BoujeeEnjinia1701/picoflow/cad/drawings/PCF-DWG-101.pdf

### BUILD PLAN SKETCH, PLAN NOT YET BUILT PicoFlow · github.com/BoujeeEnjinia1701/picoflow

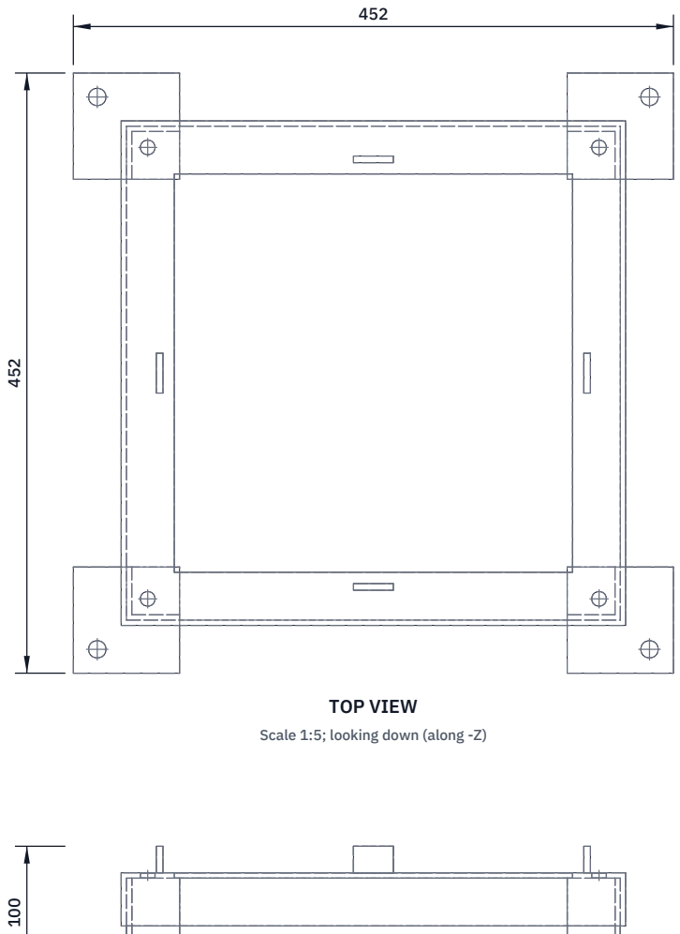
[picture p7: figure]
TOP VIEW; Scale 1:5; looking down (along -Z)

FRONT VIEW
Scale 1:5; looking at the front (along +Y)

RIGHT VIEW
Scale 1:5; looking at the right side (along -X)

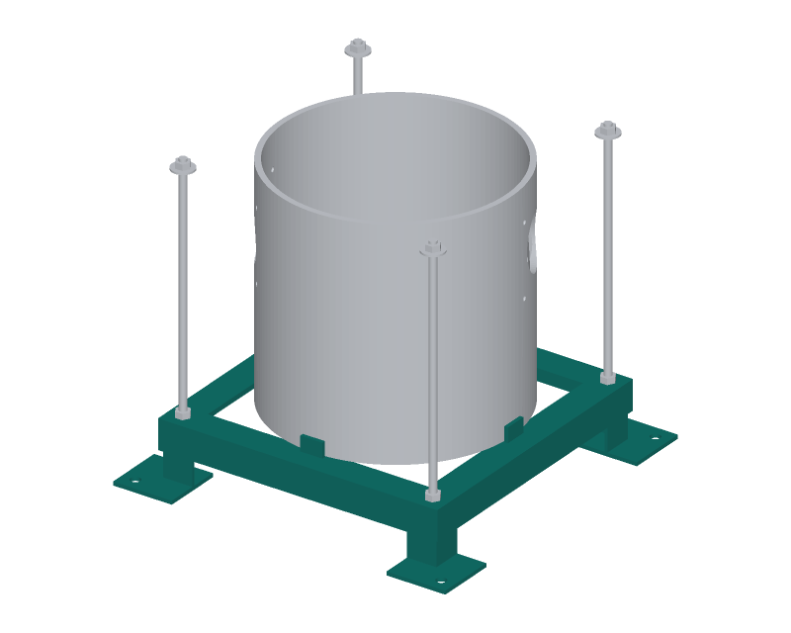
[picture p8: figure]

WHERE IT GOES
This part in colour, its neighbours in grey

HOW TO MAKE IT AND HOW IT FITS
Square: four 380 mm lengths of 40 x 40 x 4 angle, mitred 45 deg at each end, horizontal legs pointing inward, top faces flat and level.
Weld the corners; check the diagonals agree within 2 mm.
Legs: four 70 mm lengths of the same angle, fitted inside each corner, tight under the horizontal legs and against the vertical legs; weld.
Feet: four 80 x 80 x 5 mm plates welded under the legs, reaching outward; one 13 mm anchor hole in each, 208 mm from the centre lines. Pipe stops: four 30 x 20 x 5 mm flat bars welded upright on the horizontal legs at the middle of each side, inner face 158.5 mm
from the centre (1 mm outside the housing).
Tie rod holes: 11 mm in each corner, 170 mm from both centre lines.
Clean the welds, then galvanize or paint the whole frame. Never weld after galvanizing. Check: top flat within 1 mm; the housing drops in between the stops.
REV | DESCRIPTION | DATE | BY
P1 | Making sketch for the prototype build plan | 2026-10-02 | AC
PICOFLOW | github.com/BoujeeEnjinia1701/picoflow

## PicoFlow turbine frame: making sketch

DRAWING NO.
PCF-DWG-101

REV
P1

SHEET
1 of 1

SIZE

## ANSI B

SCALE
1:5

UNITS
mm
PROJECTION | DATE
2026-10-02

DRAWN
Amish Chadha

MATERIAL / NOTES
Bare steel angle 40 x 40 x 4 mm; flat 80 x 80 x 5 and 30 x 20 x 5 mm; galvanized or painted after welding
Licensed CERN-OHL-S-2.0 · Design Molecule Lab · designmolecule.com | Generated from cad/src; do not edit by hand
