BoujeeEnjinia1701/picoflow/cad/drawings/PCF-DWG-102.pdf

### BUILD PLAN SKETCH, PLAN NOT YET BUILT PicoFlow · github.com/BoujeeEnjinia1701/picoflow

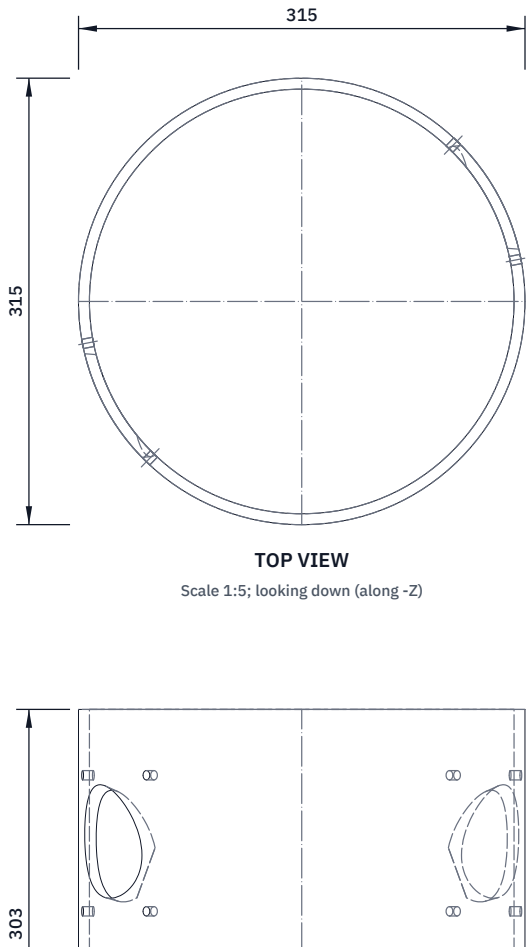
[picture p9: figure]
TOP VIEW; Scale 1:5; looking down (along -Z)

FRONT VIEW
Scale 1:5; looking at the front (along +Y)

RIGHT VIEW
Scale 1:5; looking at the right side (along -X)

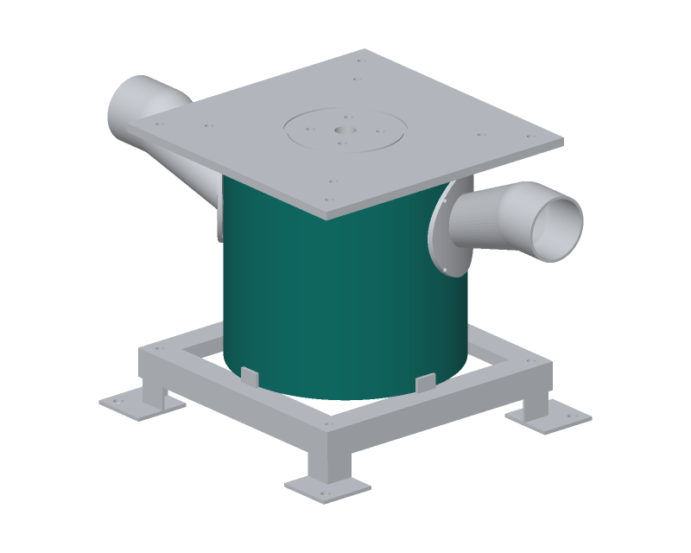
[picture p10: figure]

WHERE IT GOES
This part in colour, its neighbours in grey

HOW TO MAKE IT AND HOW IT FITS
Cut 303 mm of 315 mm pipe. Wrap a strip of card round the pipe as a guide, saw square with a fine-tooth saw, and file both ends flat.
Two nozzle holes, on opposite sides, each with four bolt holes. Tape the full-size template (nozzle hole template) to the pipe: its centre line
is 208.6 mm up from the bottom end; the second hole is the same, turned half a turn round the pipe.
Chain drill inside the hole outline with 6 mm, cut out with a jigsaw, file to the line. Drill the eight bolt holes 6.6 mm square to the wall. The holes are larger than the nozzle tip by 2.5 mm all round; the nozzle saddle and its gasket cover them.
The 3 mm at the top sits in the groove under the lid.
Check: each nozzle passes through its hole without touching the edge.
REV | DESCRIPTION | DATE | BY
P1 | Making sketch for the prototype build plan | 2026-10-02 | AC
PICOFLOW | github.com/BoujeeEnjinia1701/picoflow

## PicoFlow housing: making sketch

DRAWING NO.
PCF-DWG-102

REV
P1

SHEET
1 of 1

SIZE

## ANSI B

SCALE
1:5

UNITS
mm
PROJECTION | DATE
2026-10-02

DRAWN
Amish Chadha

MATERIAL / NOTES
315 mm PVC sewer pipe, SN4 (7.7 mm wall)
Licensed CERN-OHL-S-2.0 · Design Molecule Lab · designmolecule.com | Generated from cad/src; do not edit by hand
