BoujeeEnjinia1701/picoflow/cad/drawings/PCF-DWG-103.pdf

### BUILD PLAN SKETCH, PLAN NOT YET BUILT PicoFlow · github.com/BoujeeEnjinia1701/picoflow

FRONT VIEW
Scale 1:5; looking at the front (along +Y)

TOP VIEW
Scale 1:5; looking down (along -Z)

RIGHT VIEW
Scale 1:5; looking at the right side (along -X)

244

130 167

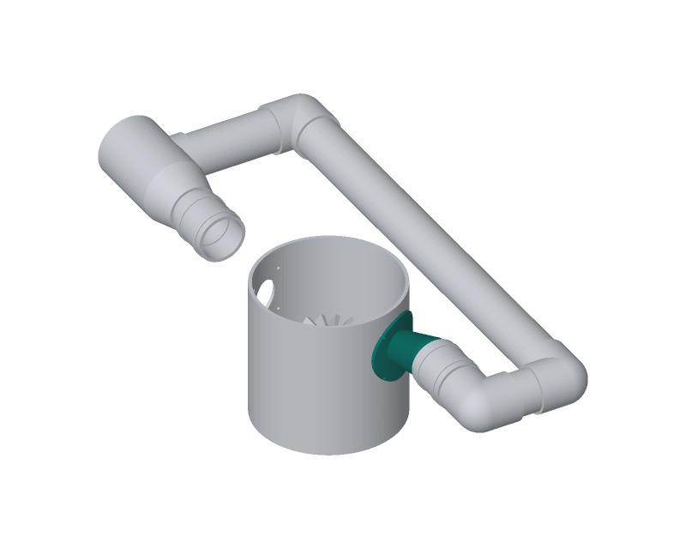
[picture p11: figure]

WHERE IT GOES
This part in colour, its neighbours in grey

HOW TO MAKE IT AND HOW IT FITS
Print two from the model file (cad/step/picoflow-nozzle.step). They are the same part: jet 2's nozzle is jet 1's turned half a turn.
Print standing on the spigot end, with supports under the saddle;
the part fits a 167 x 130 x 244 mm space, about 300 g and 12 h each. Spigot: 90 mm outside, 60 mm long, horizontal. A gentle 20 deg bend turns the nozzle down to the runner. Cone 170 mm long, from 90 mm to 64 mm outside. Saddle: a patch 144 mm across shaped to the housing, 6 mm thick, four 6.6 mm bolt holes.
Tip: a 50 mm seat 25 mm deep for the insert, and two 5.6 mm holes for M4 heat-set inserts, 28.5 mm each side of the centre.
Fit: the tip goes through the housing hole; the saddle sits on a 2 mm EPDM gasket, four M6 bolts, nuts inside. The spigot joins the pipe in a 90 mm flexible coupling.
Check: spigot 90 mm (fits the coupling); saddle sits on the pipe.
REV | DESCRIPTION | DATE | BY
P1 | Making sketch for the prototype build plan | 2026-10-02 | AC
PICOFLOW | github.com/BoujeeEnjinia1701/picoflow

## PicoFlow nozzle (make 2, both the same): making sketch

DRAWING NO.
PCF-DWG-103

REV
P1

SHEET
1 of 1

SIZE

## ANSI B

SCALE
1:5

UNITS
mm
PROJECTION | DATE
2026-10-02

DRAWN
Amish Chadha

MATERIAL / NOTES
PETG, 3D printed, 4 mm walls, 40 % infill
Licensed CERN-OHL-S-2.0 · Design Molecule Lab · designmolecule.com | Generated from cad/src; do not edit by hand
