BoujeeEnjinia1701/picoflow/cad/drawings/PCF-DWG-104.pdf

### BUILD PLAN SKETCH, PLAN NOT YET BUILT PicoFlow · github.com/BoujeeEnjinia1701/picoflow

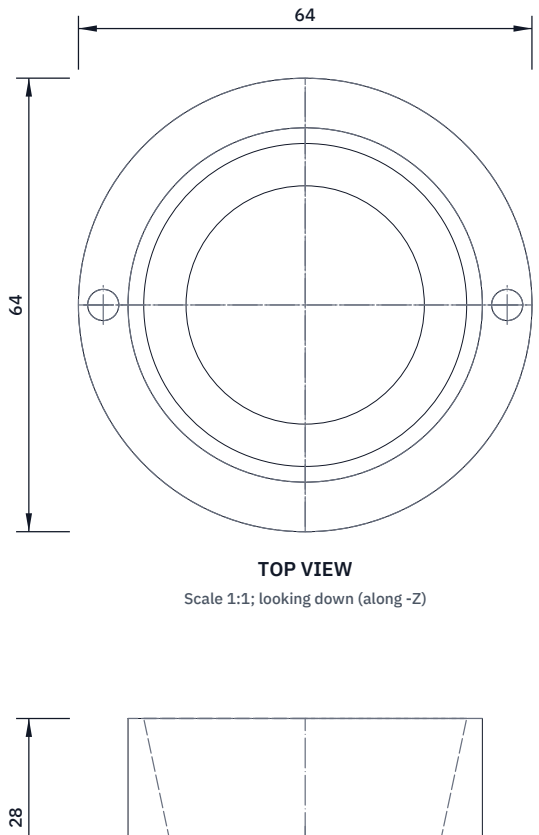
[picture p12: figure]
TOP VIEW; Scale 1:1; looking down (along -Z)

FRONT VIEW
Scale 1:1; looking at the front (along +Y)

RIGHT VIEW
Scale 1:1; looking at the right side (along -X)

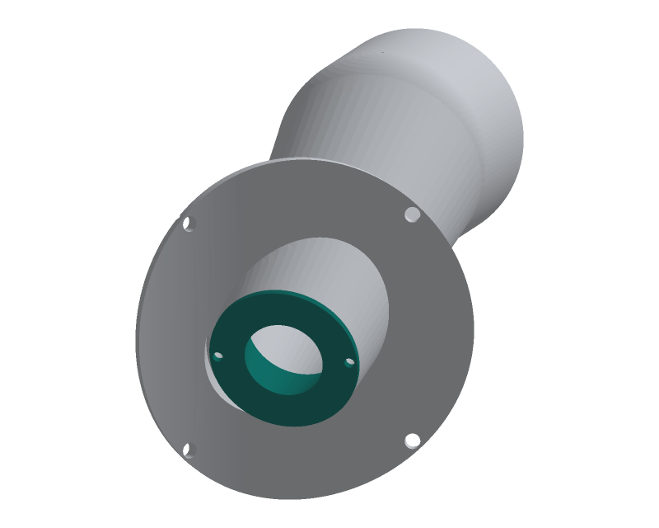
[picture p13: figure]

WHERE IT GOES
This part in colour, its neighbours in grey

HOW TO MAKE IT AND HOW IT FITS
Print a pair for each size used: 34 mm bore for the design point.
A set from 20 to 45 mm covers the head and flow range.
Body: 50 mm outside, 25 mm long, fits the seat in the nozzle tip. Flange: 64 mm across, 3 mm thick, with two 4.4 mm holes 57 mm apart. Bore: converges smoothly from 46 mm at the back to the jet size at
the front face; the last few millimetres must be round and sharp.
Print with the front face down on the bed so the jet edge is clean.
Ream or sand the bore to size; check it with a caliper.
Fit: slide into the nozzle tip from inside the housing, two M4 screws into the heat-set inserts.
Check: the bore is within 0.2 mm of size and round.
REV | DESCRIPTION | DATE | BY
P1 | Making sketch for the prototype build plan | 2026-10-02 | AC
PICOFLOW | github.com/BoujeeEnjinia1701/picoflow

## PicoFlow nozzle insert (make 2 per size): making sketch

DRAWING NO.
PCF-DWG-104

REV
P1

SHEET
1 of 1

SIZE

## ANSI B

SCALE
1:1

UNITS
mm
PROJECTION | DATE
2026-10-02

DRAWN
Amish Chadha

MATERIAL / NOTES
PETG, 3D printed, 100 % infill
Licensed CERN-OHL-S-2.0 · Design Molecule Lab · designmolecule.com | Generated from cad/src; do not edit by hand
