BoujeeEnjinia1701/picoflow/cad/drawings/PCF-DWG-105.pdf

### BUILD PLAN SKETCH, PLAN NOT YET BUILT PicoFlow · github.com/BoujeeEnjinia1701/picoflow

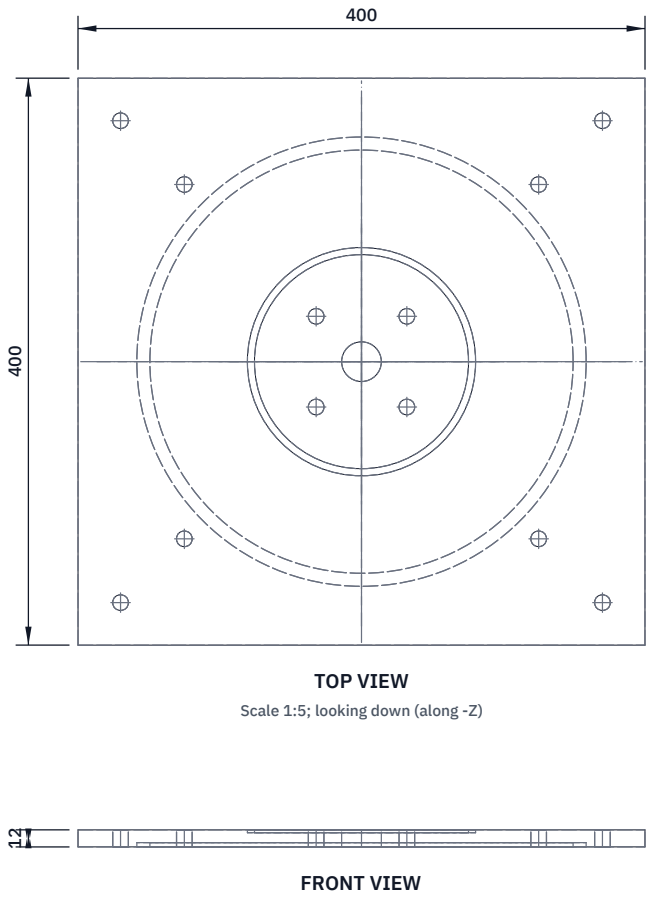
[picture p14: figure]
FRONT VIEW; TOP VIEW; Scale 1:5; looking down (along -Z)

Scale 1:5; looking at the front (along +Y)

RIGHT VIEW
Scale 1:5; looking at the right side (along -X)

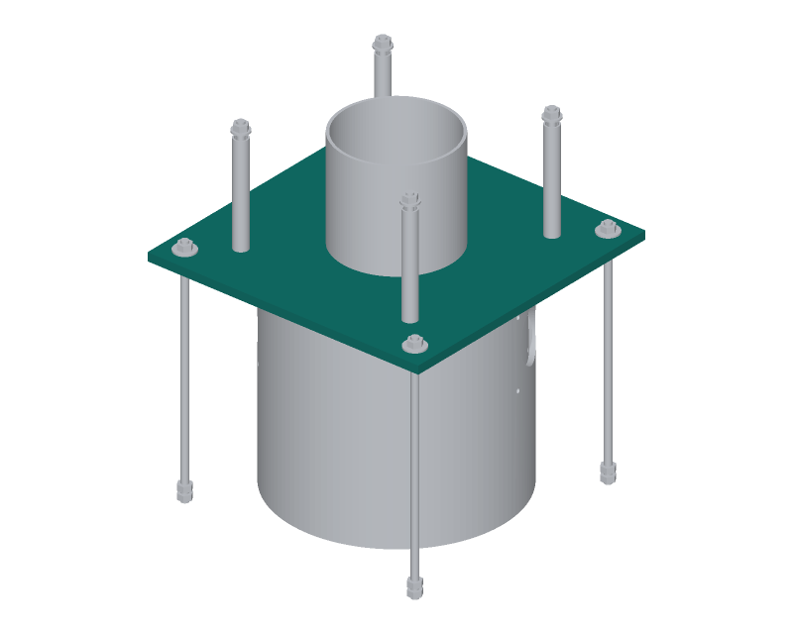
[picture p15: figure]

WHERE IT GOES
This part in colour, its neighbours in grey

HOW TO MAKE IT AND HOW IT FITS
Cut 400 x 400 mm; round the corners to about 5 mm.
Holes from the centre (the lid hole layout figure gives all of them): shaft 28 mm in the centre; bearing bolts 11 mm at 32 each way;
post rods 11 mm at 125 each way; tie rods 11 mm at 170 each way. Underneath: a ring groove 3 mm deep, 148.8 to 158.5 mm radius, that the top of the housing sits in. Rout with a trammel jig.
On top: a ring groove 2 mm deep, 75.5 to 80.5 mm radius, for the guard. Mark the two grooves from the same centre as the shaft hole.
Fit: housing in the lower groove; lower bearing unit, posts and guard on top; four tie rods through the corners with washers and nuts.
Check: the lid drops onto the housing and the groove takes the whole rim without forcing.
REV | DESCRIPTION | DATE | BY
P1 | Making sketch for the prototype build plan | 2026-10-02 | AC
PICOFLOW | github.com/BoujeeEnjinia1701/picoflow

## PicoFlow lid: making sketch

DRAWING NO.
PCF-DWG-105

REV
P1

SHEET
1 of 1

SIZE

## ANSI B

SCALE
1:5

UNITS
mm
PROJECTION | DATE
2026-10-02

DRAWN
Amish Chadha

MATERIAL / NOTES
HDPE sheet 12 mm (or marine plywood, sealed)
Licensed CERN-OHL-S-2.0 · Design Molecule Lab · designmolecule.com | Generated from cad/src; do not edit by hand
