BoujeeEnjinia1701/picoflow/cad/drawings/PCF-DWG-106.pdf

### BUILD PLAN SKETCH, PLAN NOT YET BUILT PicoFlow · github.com/BoujeeEnjinia1701/picoflow

FRONT VIEW
Scale 1:2; looking at the front (along +Y)

TOP VIEW
Scale 1:2; looking down (along -Z)

RIGHT VIEW
Scale 1:2; looking at the right side (along -X)

294

20 20

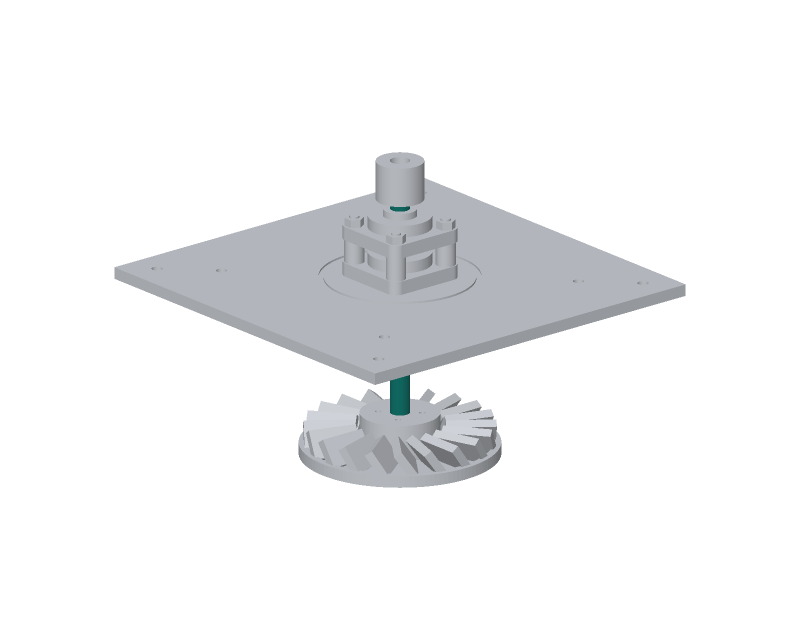
[picture p16: figure]

WHERE IT GOES
This part in colour, its neighbours in grey

HOW TO MAKE IT AND HOW IT FITS
Cut 294 mm of 20 mm ground stainless bar; face both ends square and chamfer them 1 mm so the bearings slide on.
Check the bar slides through a bearing unit by hand; polish any burr with fine emery.
No keyways: the runner hub and coupling clamp the shaft, and the bearing inserts lock with their own set screws.
At assembly, spot each set screw into the shaft with a 5 mm drill 0.5 mm deep through the screw hole, then tighten.
Fit: bottom end flush with the underside of the runner hub; top end half way into the jaw coupling, 30 mm above the upper bearing. Check: straight within 0.1 mm over its length (roll it on glass).
REV | DESCRIPTION | DATE | BY
P1 | Making sketch for the prototype build plan | 2026-10-02 | AC
PICOFLOW | github.com/BoujeeEnjinia1701/picoflow

## PicoFlow shaft: making sketch

DRAWING NO.
PCF-DWG-106

REV
P1

SHEET
1 of 1

SIZE

## ANSI B

SCALE
1:2

UNITS
mm
PROJECTION | DATE
2026-10-02

DRAWN
Amish Chadha

MATERIAL / NOTES
316 stainless steel bar, 20 mm, h9 or ground
Licensed CERN-OHL-S-2.0 · Design Molecule Lab · designmolecule.com | Generated from cad/src; do not edit by hand
