BoujeeEnjinia1701/picoflow/cad/drawings/PCF-DWG-107.pdf

### BUILD PLAN SKETCH, PLAN NOT YET BUILT PicoFlow · github.com/BoujeeEnjinia1701/picoflow

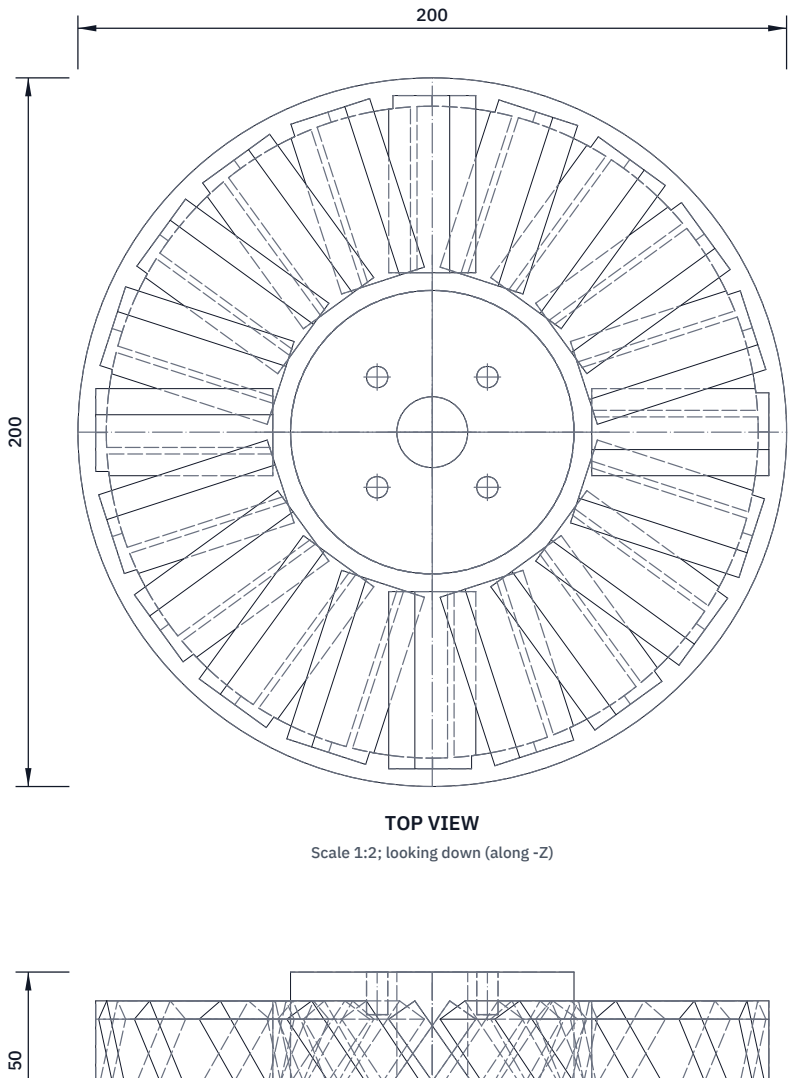
[picture p17: figure]
TOP VIEW; Scale 1:2; looking down (along -Z)

FRONT VIEW
Scale 1:2; looking at the front (along +Y)

RIGHT VIEW
Scale 1:2; looking at the right side (along -X)

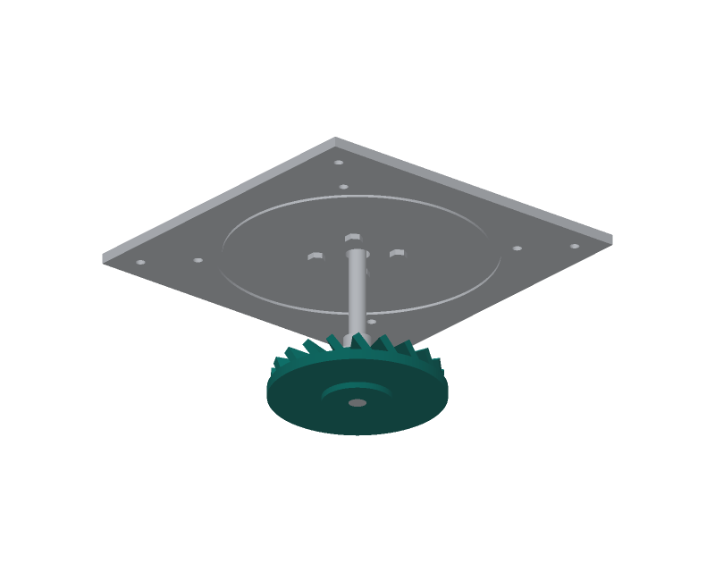
[picture p18: figure]

WHERE IT GOES
This part in colour, its neighbours in grey

HOW TO MAKE IT AND HOW IT FITS
Print from the model file (cad/step/picoflow-runner.step), hub down, with supports under the buckets. 200 mm across, 50 mm tall,
about 525 g and 21 h at 0.4 mm; four perimeters.
20 buckets on a 150 mm pitch circle; the jets strike the top of the bucket band, which is 17 mm above the runner's mid-height.
Hub: 80 mm across, 50 mm tall, 20 mm bore. Ream the bore to slide on the shaft. Press four M5 heat-set inserts into the hub top on
a 44 mm circle with a soldering iron.
Balance: hang the runner on a rod through the bore; if one side always drops, sand the bucket backs on that side lightly.
Fit: the clamping hub bolts to the hub top with four M5 screws. Check: the runner spins on a rod and stops in random places.
REV | DESCRIPTION | DATE | BY
P1 | Making sketch for the prototype build plan | 2026-10-02 | AC
PICOFLOW | github.com/BoujeeEnjinia1701/picoflow

## PicoFlow Turgo runner: making sketch

DRAWING NO.
PCF-DWG-107

REV
P1

SHEET
1 of 1

SIZE

## ANSI B

SCALE
1:2

UNITS
mm
PROJECTION | DATE
2026-10-02

DRAWN
Amish Chadha

MATERIAL / NOTES
PETG (prototype), glass-filled nylon (field)
Licensed CERN-OHL-S-2.0 · Design Molecule Lab · designmolecule.com | Generated from cad/src; do not edit by hand
