BoujeeEnjinia1701/picoflow/cad/drawings/PCF-DWG-108.pdf

### BUILD PLAN SKETCH, PLAN NOT YET BUILT PicoFlow · github.com/BoujeeEnjinia1701/picoflow

FRONT VIEW
Scale 1:5; looking at the front (along +Y)

TOP VIEW
Scale 1:5; looking down (along -Z)

RIGHT VIEW
Scale 1:5; looking at the right side (along -X)

160

160 146

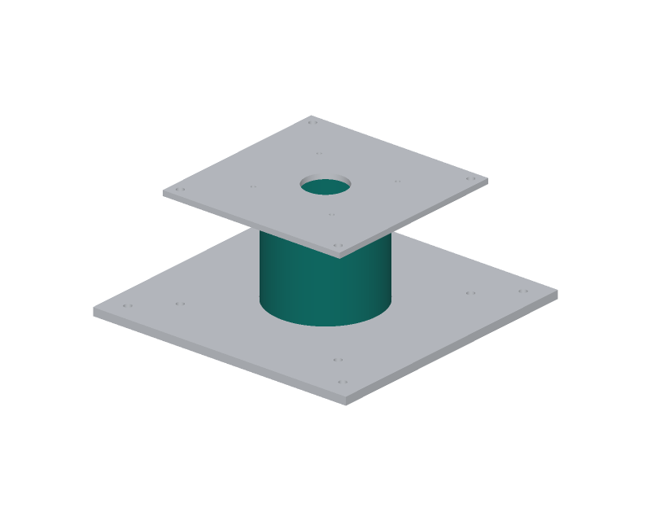
[picture p19: figure]

WHERE IT GOES
This part in colour, its neighbours in grey

HOW TO MAKE IT AND HOW IT FITS
Cut 146 mm of 160 mm pipe; saw square, file both ends flat and deburr inside.
Drill two 6 mm holes at the bottom edge, on opposite sides, so any water that gets in drains out.
Fit: the bottom end stands in the 2 mm groove on top of the lid; the top end stops 1 mm under the generator plate, which holds it in place. It covers both bearing units and the jaw coupling; nothing that turns can be reached while the plate is on.
Check: it stands in the groove and the plate clears it.
REV | DESCRIPTION | DATE | BY
P1 | Making sketch for the prototype build plan | 2026-10-02 | AC
PICOFLOW | github.com/BoujeeEnjinia1701/picoflow

## PicoFlow bearing and coupling guard: making sketch

DRAWING NO.
PCF-DWG-108

REV
P1

SHEET
1 of 1

SIZE

## ANSI B

SCALE
1:5

UNITS
mm
PROJECTION | DATE
2026-10-02

DRAWN
Amish Chadha

MATERIAL / NOTES
160 mm PVC pipe, 4 mm wall
Licensed CERN-OHL-S-2.0 · Design Molecule Lab · designmolecule.com | Generated from cad/src; do not edit by hand
