BoujeeEnjinia1701/picoflow/cad/drawings/PCF-DWG-109.pdf

### BUILD PLAN SKETCH, PLAN NOT YET BUILT PicoFlow · github.com/BoujeeEnjinia1701/picoflow

FRONT VIEW
Scale 1:2; looking at the front (along +Y)

TOP VIEW
Scale 1:2; looking down (along -Z)

RIGHT VIEW
Scale 1:2; looking at the right side (along -X)

20

20 145

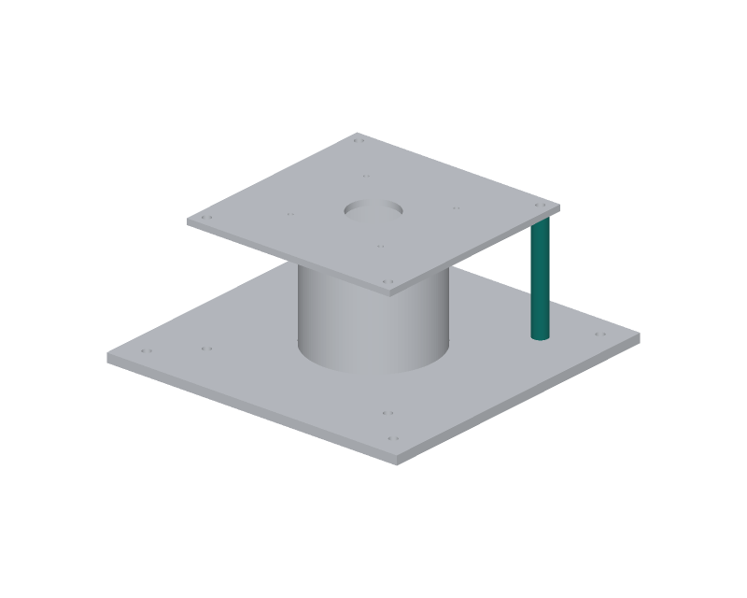
[picture p20: figure]

WHERE IT GOES
This part in colour, its neighbours in grey

HOW TO MAKE IT AND HOW IT FITS
Posts: cut four 145.0 mm lengths of 20 x 2 mm steel tube. Face the ends square on a disc sander; all four the same within 0.2 mm,
so the plate sits level.
Post rods: cut four 195 mm lengths of M10 rod; clean the thread ends. Bearing spacer sleeves: cut four 24.0 mm lengths of 20 mm tube with a 10.5 mm or larger bore, the same within 0.1 mm.
Tie rods: cut four 345 mm lengths of M10 rod.
Paint or galvanize the cut ends.
Fit: each post stands on the lid at 125 mm each way from the centre; the rod goes up from under the lid, through the post and the plate, with a 30 mm washer and nut under the lid and a washer and nut on the plate.
Check: the four posts stand the same height on a flat surface.
REV | DESCRIPTION | DATE | BY
P1 | Making sketch for the prototype build plan | 2026-10-02 | AC
PICOFLOW | github.com/BoujeeEnjinia1701/picoflow

## PicoFlow post and spacer sleeve (make 4 of each): making sketch

DRAWING NO.
PCF-DWG-109

REV
P1

SHEET
1 of 1

SIZE

## ANSI B

SCALE
1:2

UNITS
mm
PROJECTION | DATE
2026-10-02

DRAWN
Amish Chadha

MATERIAL / NOTES
Steel tube 20 x 2 mm; M10 threaded rod
Licensed CERN-OHL-S-2.0 · Design Molecule Lab · designmolecule.com | Generated from cad/src; do not edit by hand
