BoujeeEnjinia1701/picoflow/cad/drawings/PCF-DWG-110.pdf

### BUILD PLAN SKETCH, PLAN NOT YET BUILT PicoFlow · github.com/BoujeeEnjinia1701/picoflow

FRONT VIEW
Scale 1:5; looking at the front (along +Y)

TOP VIEW
Scale 1:5; looking down (along -Z)

RIGHT VIEW
Scale 1:5; looking at the right side (along -X)

280

280 8

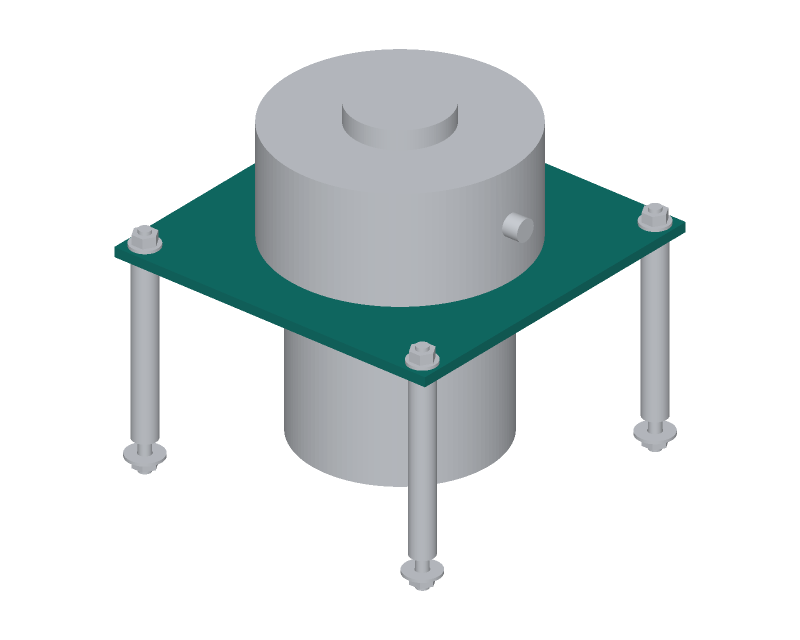
[picture p21: figure]

WHERE IT GOES
This part in colour, its neighbours in grey

HOW TO MAKE IT AND HOW IT FITS
Cut 280 x 280 mm; file the edges and round the corners. Centre hole 62 mm for the generator shaft and spigot (check the generator: the hole must clear its spigot by 1 mm).
Post holes 11 mm at 125 mm each way from the centre.
Generator screw holes 6.6 mm on a 176 mm circle at 45 deg (the model's figure; copy the circle and angle from the generator bought).
Mark the centre from the diagonals so the shaft lines up with the bearings below.
Fit: sits on the four posts, nuts on top; generator on top, four M6 screws from below; the guard stops 1 mm under it.
Check: the plate sits on all four posts without rocking.
REV | DESCRIPTION | DATE | BY
P1 | Making sketch for the prototype build plan | 2026-10-02 | AC
PICOFLOW | github.com/BoujeeEnjinia1701/picoflow

## PicoFlow generator plate: making sketch

DRAWING NO.
PCF-DWG-110

REV
P1

SHEET
1 of 1

SIZE

## ANSI B

SCALE
1:5

UNITS
mm
PROJECTION | DATE
2026-10-02

DRAWN
Amish Chadha

MATERIAL / NOTES
Aluminium plate 8 mm, 5083 or 6082
Licensed CERN-OHL-S-2.0 · Design Molecule Lab · designmolecule.com | Generated from cad/src; do not edit by hand
