BoujeeEnjinia1701/picoflow/cad/drawings/PCF-DWG-111.pdf

### BUILD PLAN SKETCH, PLAN NOT YET BUILT PicoFlow · github.com/BoujeeEnjinia1701/picoflow

FRONT VIEW
Scale 1:5; looking at the front (along +Y)

TOP VIEW
Scale 1:5; looking down (along -Z)

RIGHT VIEW
Scale 1:5; looking at the right side (along -X)

100

100 386

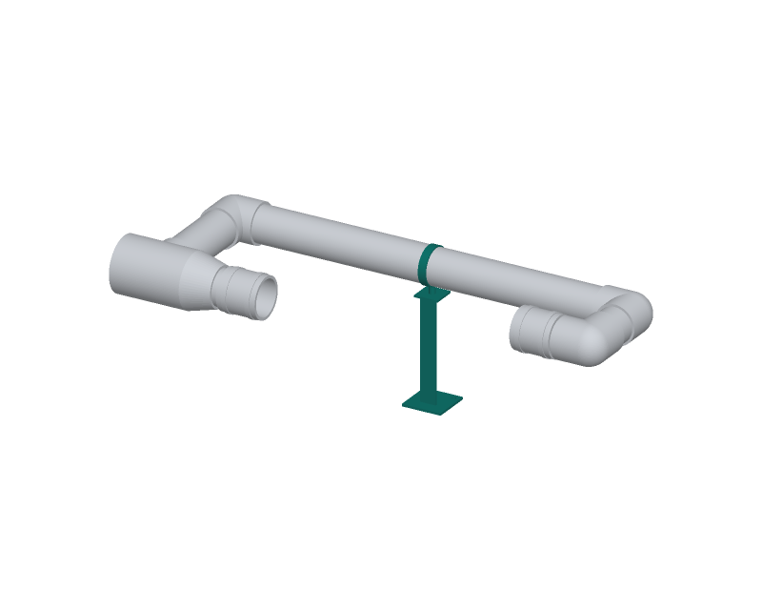
[picture p22: figure]

WHERE IT GOES
This part in colour, its neighbours in grey

HOW TO MAKE IT AND HOW IT FITS
Upright: 259 mm of 40 x 40 x 4 angle, ends square.
Foot: 100 x 100 x 6 mm plate, one 11 mm anchor hole 35 mm in from two edges; weld the upright to it in the middle, square.
Top: 60 x 60 x 5 mm plate with a 9 mm hole in the middle, welded square on top of the upright.
Clip: a 90 mm pipe clip with an M8 boss, screwed onto an
M8 bolt up through the top plate. The clip's band holds the pipe. Height: pad to the bottom of the pipe 290 mm; adjust on the M8 thread if the pad is uneven.
Fit: one under the tee branch, one under the long run, one under the short drop to jet 1 (overview); M10 anchors in the pad. Check: the pipe sits in the clip without being pushed up or down.
REV | DESCRIPTION | DATE | BY
P1 | Making sketch for the prototype build plan | 2026-10-02 | AC
PICOFLOW | github.com/BoujeeEnjinia1701/picoflow

## PicoFlow pipe stand (make 3): making sketch

DRAWING NO.
PCF-DWG-111

REV
P1

SHEET
1 of 1

SIZE

## ANSI B

SCALE
1:5

UNITS
mm
PROJECTION | DATE
2026-10-02

DRAWN
Amish Chadha

MATERIAL / NOTES
Bare steel angle 40 x 40 x 4 mm, flat 100 x 100 x 6 and 60 x 60 x 5 mm; galvanized or painted after welding
Licensed CERN-OHL-S-2.0 · Design Molecule Lab · designmolecule.com | Generated from cad/src; do not edit by hand
