BoujeeEnjinia1701/picoflow/cad/drawings/PCF-DWG-112.pdf

### BUILD PLAN SKETCH, PLAN NOT YET BUILT PicoFlow · github.com/BoujeeEnjinia1701/picoflow

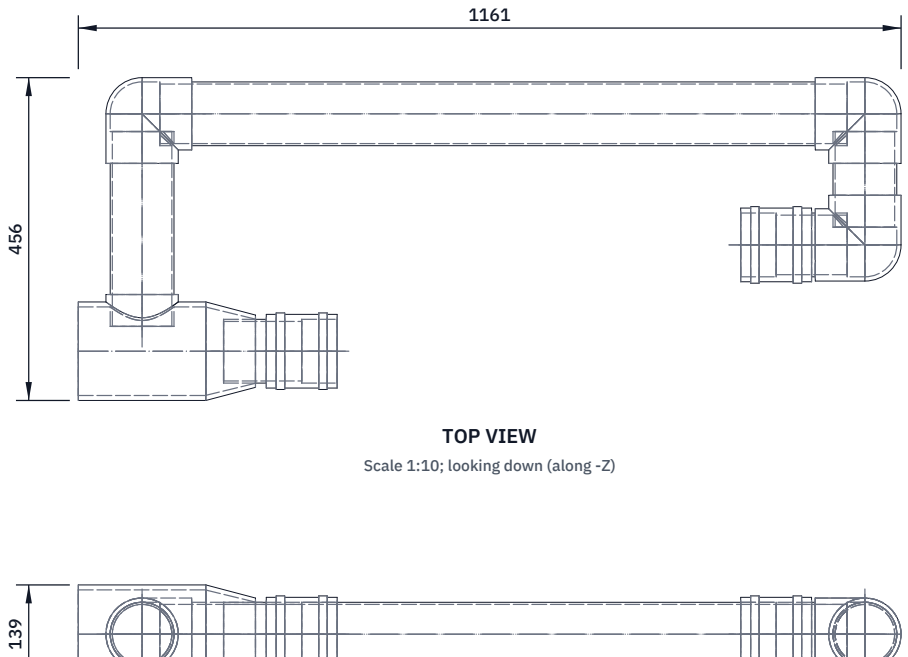
[picture p23: figure]
TOP VIEW; Scale 1:10; looking down (along -Z)

FRONT VIEW
Scale 1:10; looking at the front (along +Y)

RIGHT VIEW
Scale 1:10; looking at the right side (along -X)

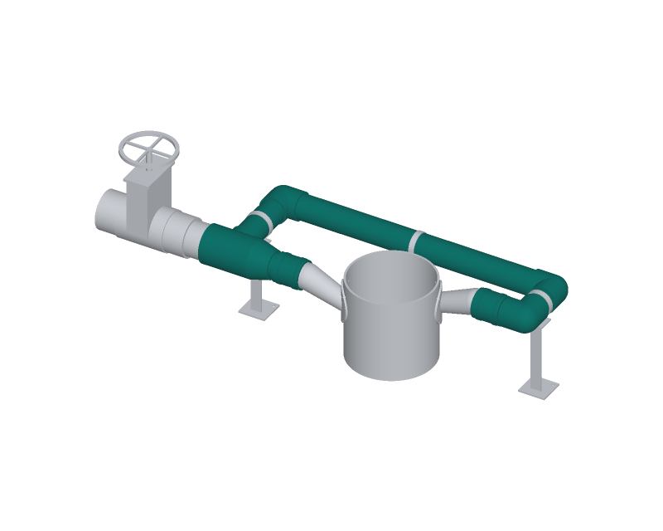
[picture p24: figure]

WHERE IT GOES
This part in colour, its neighbours in grey

HOW TO MAKE IT AND HOW IT FITS
Cut five lengths of 90 mm pipe (for sockets 45 mm deep; adjust each by the difference if your fittings differ):
P1 tee branch to first elbow, 275 mm; P2 long run, 970 mm;
P3 short drop, 135 mm; P4 last elbow to jet 1 coupling, 100 mm;
P5 reducer to jet 2 coupling, 110 mm.
The valve's pipe piece enters the 125 mm run of the tee; the other end takes a 125 x 90 reducer and P5 to jet 2. The 90 mm side branch takes
P1, then elbows and P2, P3, P4 round the housing to jet 1.
Dry fit everything on the stands first. Then solvent weld the PVC
joints, one at a time, keeping the elbows square.
Flexible couplings join P4 and P5 to the nozzle spigots; band clamps snug, not crushed. Do not glue the nozzles.
Check: centre line 338 mm above the pad all round.
REV | DESCRIPTION | DATE | BY
P1 | Making sketch for the prototype build plan | 2026-10-02 | AC
PICOFLOW | github.com/BoujeeEnjinia1701/picoflow

## PicoFlow nozzle manifold pipework: cutting and fitting sketch

DRAWING NO.
PCF-DWG-112

REV
P1

SHEET
1 of 1

SIZE

## ANSI B

SCALE
1:10

UNITS
mm
PROJECTION | DATE
2026-10-02

DRAWN
Amish Chadha

MATERIAL / NOTES
90 mm PVC pipe and fittings; 125 x 90 mm reducing tee and reducer
Licensed CERN-OHL-S-2.0 · Design Molecule Lab · designmolecule.com | Generated from cad/src; do not edit by hand
