BoujeeEnjinia1701/picoflow/cad/drawings/PCF-DWG-113.pdf

### BUILD PLAN SKETCH, PLAN NOT YET BUILT PicoFlow · github.com/BoujeeEnjinia1701/picoflow

FRONT VIEW
Scale 1:10; looking at the front (along +Y)

TOP VIEW
Scale 1:10; looking down (along -Z)

RIGHT VIEW
Scale 1:10; looking at the right side (along -X)

660

500 420

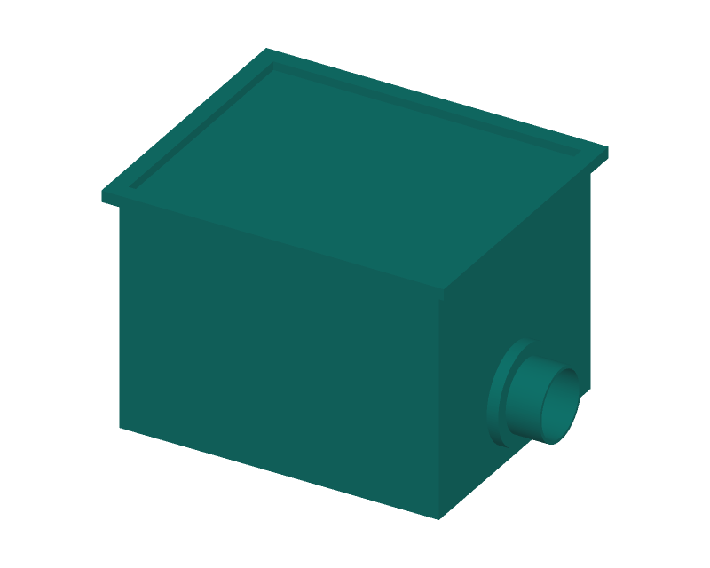
[picture p25: figure]

WHERE IT GOES
This part in colour, its neighbours in grey

HOW TO MAKE IT AND HOW IT FITS
Tub: about 560 x 460 x 400 mm outside, stiff polyethylene.
Outlet: 128 mm hole centred 110 mm up in the downstream end, for a 125 mm tank connector (gasket inside, nut outside).
Overflow: cut a notch 200 mm wide and 40 mm deep in the upstream rim, so surplus water and leaves run off away from the outlet.
Screen frame: 20 x 20 x 3 mm aluminium angle, 600 x 500 mm outside, mitred and riveted; it rests on the rim and overlaps it
by 10 mm all round.
Screen: 6 mm stainless mesh cut to 580 x 480 mm, riveted to the frame. The stream is led onto the screen; water drops through, surplus runs over and carries leaves away.
Check: no gap larger than 6 mm anywhere round the screen.
REV | DESCRIPTION | DATE | BY
P1 | Making sketch for the prototype build plan | 2026-10-02 | AC
PICOFLOW | github.com/BoujeeEnjinia1701/picoflow

## PicoFlow forebay tub and intake screen: making sketch

DRAWING NO.
PCF-DWG-113

REV
P1

SHEET
1 of 1

SIZE

## ANSI B

SCALE
1:10

UNITS
mm
PROJECTION | DATE
2026-10-02

DRAWN
Amish Chadha

MATERIAL / NOTES
Polyethylene tub; 6 mm stainless mesh; aluminium angle 20 x 20 x 3 mm
Licensed CERN-OHL-S-2.0 · Design Molecule Lab · designmolecule.com | Generated from cad/src; do not edit by hand
