BoujeeEnjinia1701/picoflow/cad/drawings/PCF-DWG-114.pdf

### BUILD PLAN SKETCH, PLAN NOT YET BUILT PicoFlow · github.com/BoujeeEnjinia1701/picoflow

FRONT VIEW
Scale 1:20; looking at the front (along +Y)

TOP VIEW
Scale 1:20; looking down (along -Z)

RIGHT VIEW
Scale 1:20; looking at the right side (along -X)

70

70 1400

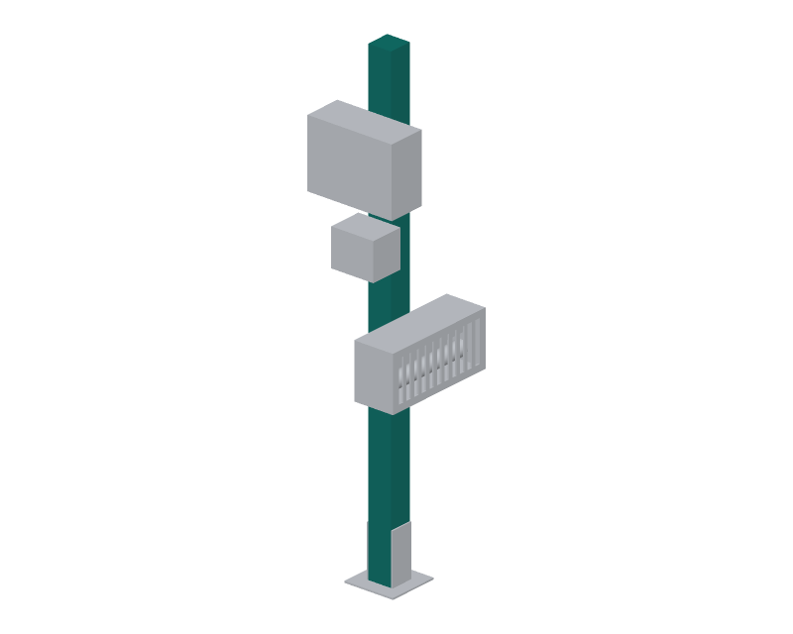
[picture p26: figure]

WHERE IT GOES
This part in colour, its neighbours in grey

HOW TO MAKE IT AND HOW IT FITS
Cut 1,400 mm of 70 x 70 mm treated timber; seal the cut ends. Bolt-down post anchor: drop the post in, drill through the anchor's side holes and bolt with two M10 coach bolts.
Mark the boxes on the front face (the face toward the turbine): rectifier box 840 to 960 mm up; controller box 1,030 to 1,230 mm. Resistor guard on the side face, 540 to 700 mm up, with 50 mm air space all round and nothing that burns within 300 mm above it.
Fix each box with four stainless screws through its own mounting holes; cable glands face down.
Site: on ground above flood level, at least 1 m from the stream bank. Check: the post stands upright and does not rock in its anchor.
REV | DESCRIPTION | DATE | BY
P1 | Making sketch for the prototype build plan | 2026-10-02 | AC
PICOFLOW | github.com/BoujeeEnjinia1701/picoflow

## PicoFlow equipment post: making sketch

DRAWING NO.
PCF-DWG-114

REV
P1

SHEET
1 of 1

SIZE

## ANSI B

SCALE
1:20

UNITS
mm
PROJECTION | DATE
2026-10-02

DRAWN
Amish Chadha

MATERIAL / NOTES
Treated timber 70 x 70 mm; bolt-down post anchor
Licensed CERN-OHL-S-2.0 · Design Molecule Lab · designmolecule.com | Generated from cad/src; do not edit by hand
