BoujeeEnjinia1701/picoflow/cad/drawings/PCF-DWG-001.png

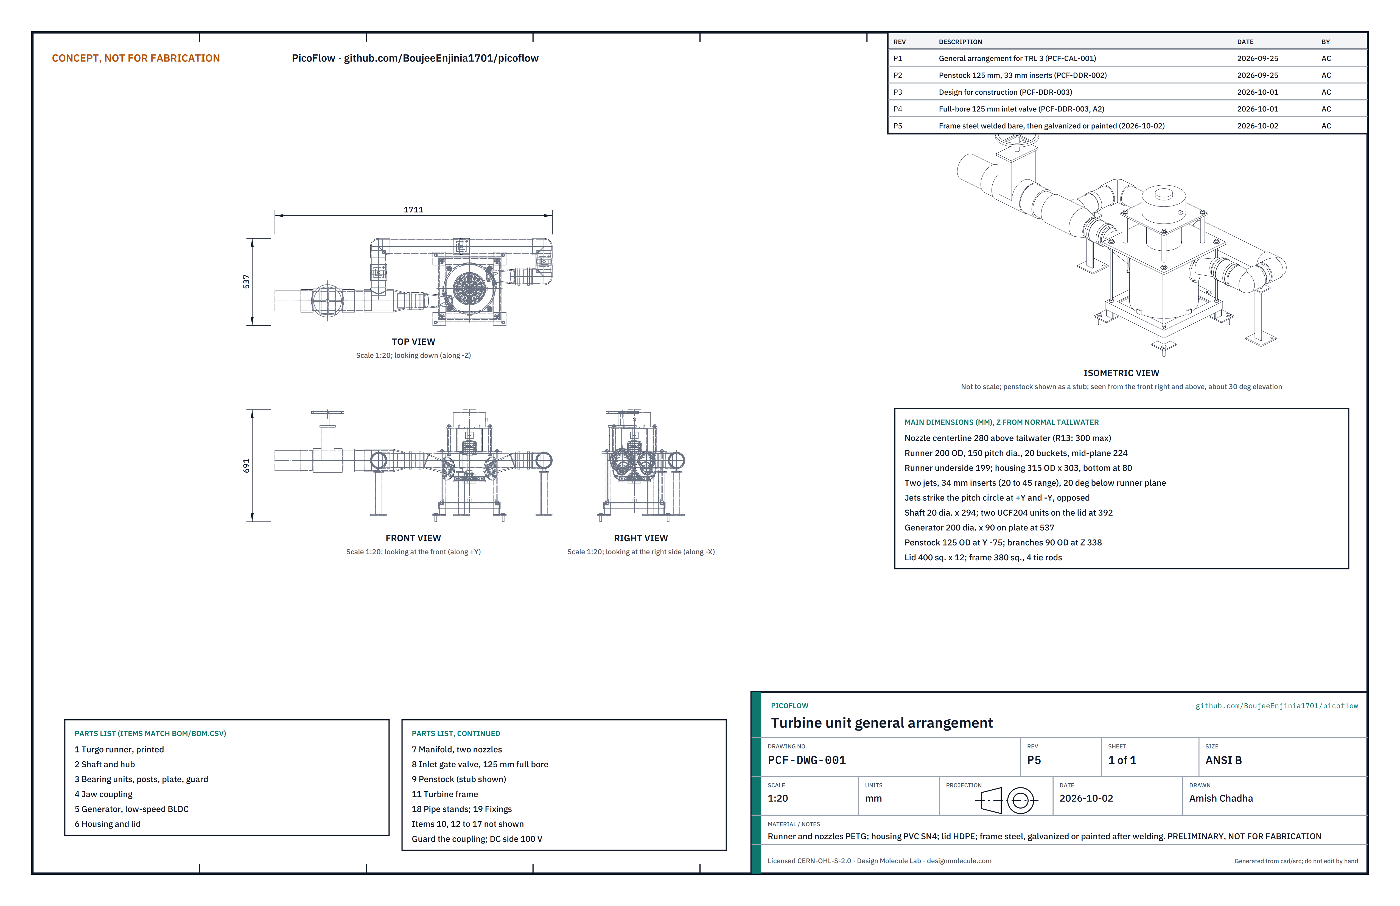
cad/drawings/PCF-DWG-001.png
