BoujeeEnjinia1701/picoflow/media/card.png

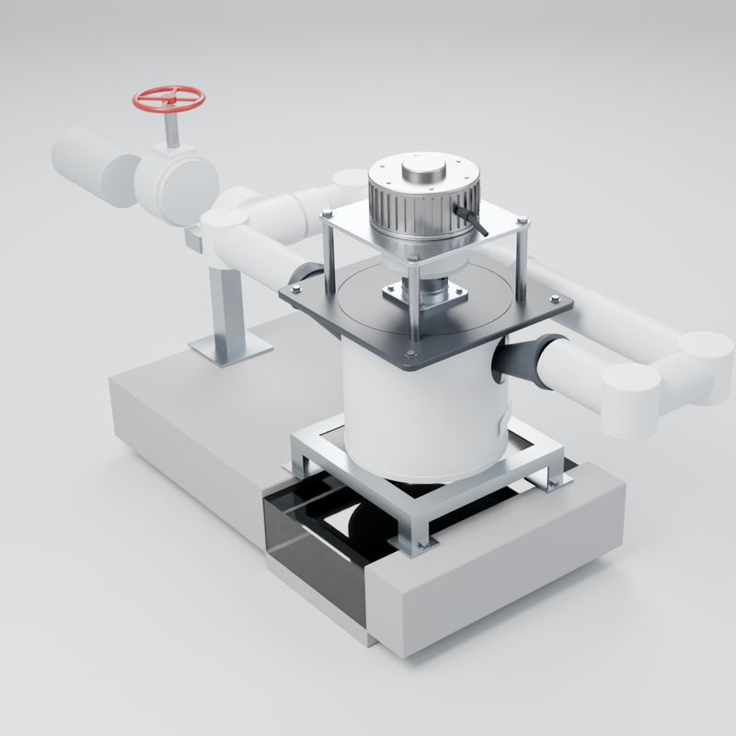
media/card.png
