BoujeeEnjinia1701/picoflow/media/concept-blueprint.png

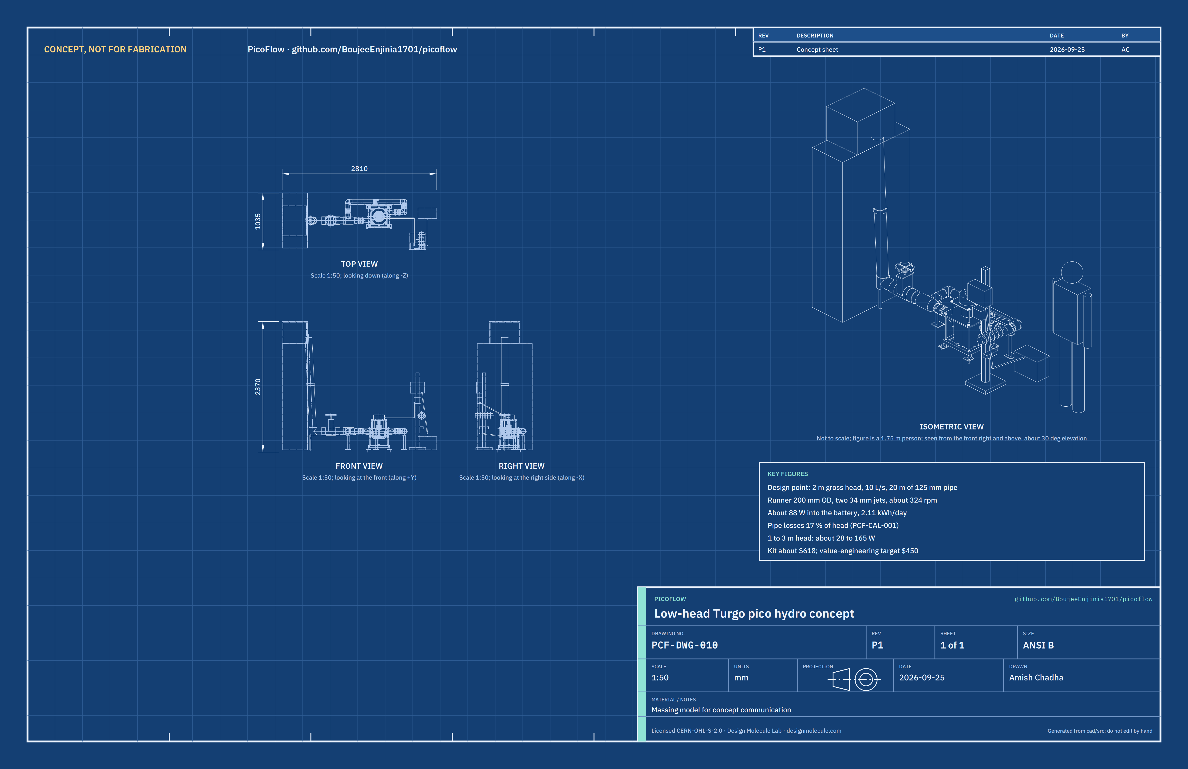
media/concept-blueprint.png
