BoujeeEnjinia1701/picoflow/media/render-detail.png

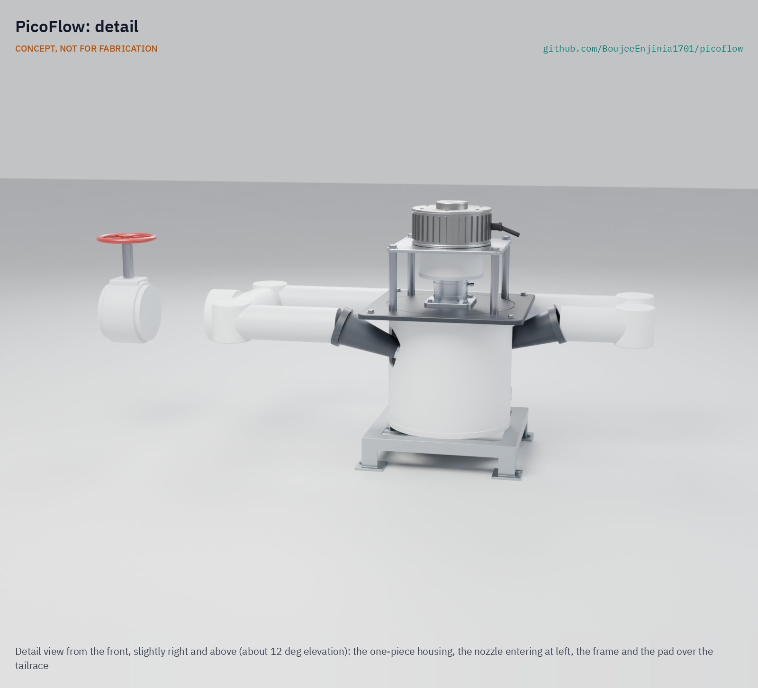
media/render-detail.png
