BoujeeEnjinia1701/picoflow/media/render-exploded.png

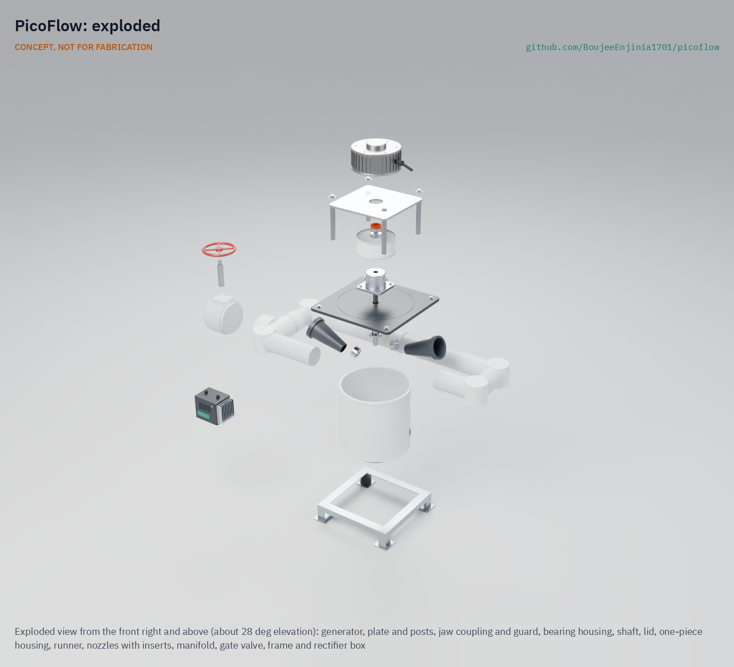
media/render-exploded.png
