BoujeeEnjinia1701/picoflow/media/social-preview.png

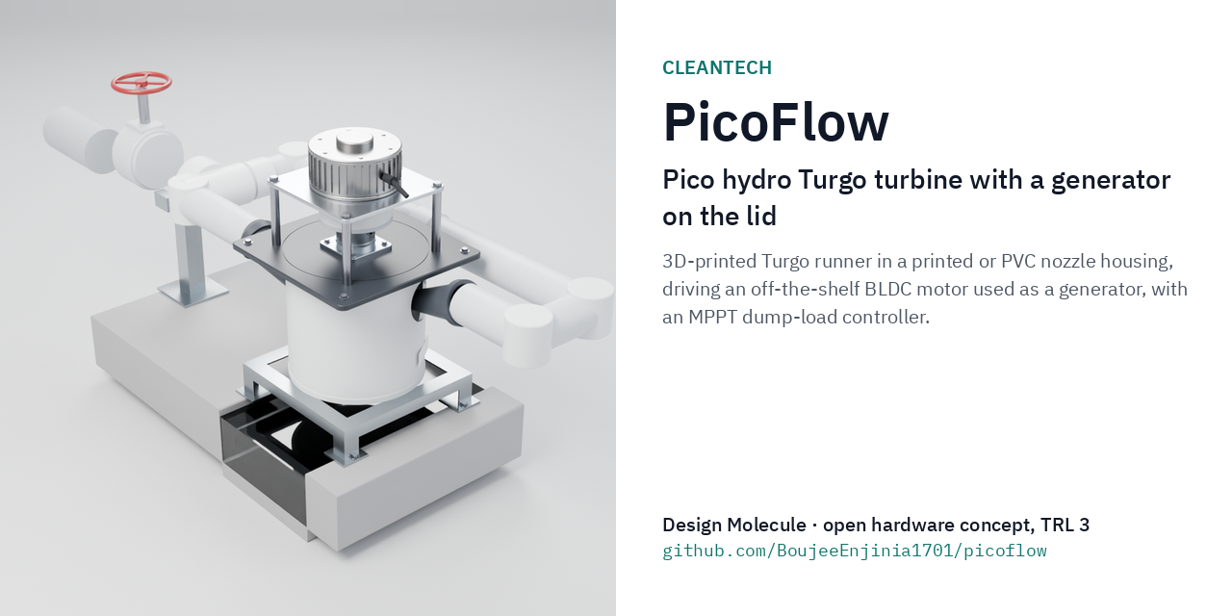
media/social-preview.png
